Sonoscopia/M-Blocks/docs/M-Blocks Connections diagram.graffle/image2.tiff

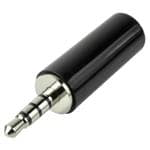
docs/M-Blocks Connections diagram.graffle/image2.tiff
