Sonoscopia/M-Blocks/testers/ReadI2C_tester/ReadI2C_tester.ino

/*  Simply read incoming I2C
 * 
 */
#include <Wire.h>

#define ADDR 8 // this device address
#define NUMBYTES 4 // number of bytes using in communication from M-Controllers to M-Brain

void setup() {
  Wire.begin(ADDR); 
  Wire.onReceive(receiveI2C);
  Serial.begin(9600);
}

void loop() {

}

void receiveI2C(int howmany){
  while(Wire.available()){
    byte v = Wire.read();
    Serial.print(v);
    Serial.print(" "); 
  }
  if(!Wire.available()) Serial.println(); // print line when no more bytes are available
}
